aztlek/ModularCockpit/modules/MovementModule/README.md

# Movement Module

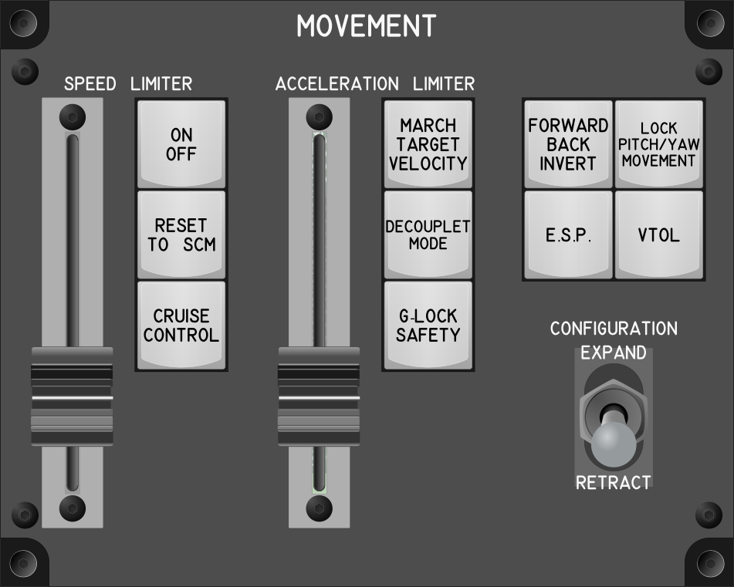
[picture p10: modules/MovementModule/images/MovementModule_150mmWidth.png]
Movement Module


## Keybindings

| Keybinding |  Key / Mouse  | Joy  | Input Device Type |
| --- | --- | ---- | --- |
| Strafe forward / back Invert | | Key  | key[0] |
| Decouplet mode (toggle) | Left Alt + C  | Key  | key[1] |
| Speed Limiter (Abs.) | | Axis | slide_pot[0] |
| Speed Limiter - On/Off (Hold/Toggle) | | Key  | key[2] |
| Speed Limiter – Reset to SCM | | Key  | key[3] |
| Acceleration Limiter Up / Down (abs.) | | Axis | slide_pot[1] |
| March target velocity | | Key  | key[4] |
| Lock Pitch / Yaw movement (toggle / hold) | Right Shift | Key  | key[5] |
| G-Lock safety On/Off (Toggle / Hold) | | Key  | key[6] |
| E.S.P. On/Off (Toggle / Hold) | | Key  | key[7] |
| @ui+v_ifcs_esp_hold | | Key  | key[8] |
| Cruise Control (Toggle) | C | Key  | key[9] |
| Toggle VTOL | K | Key  | key[10] |
| Expand Configuration | | Key  | toggle_switch[0]: On  |
| Retract Configuration | | Key  | toggle_switch[0]: Off |

### Total devices in keybindings

| Device | Count  |
| --- | -----: |
| Keys | 11 |
| Toggle switchs | 1 |
| Encoders | 0 |
| Slide Pot | 2 |
| Joystick | 0 |

## Bill of materials

| Material | Qty. | Links |
| --- | ---: | --- |
| Twidec/Heavy Duty Rocker Toggle Switch 16A 250V SPST 2 Position 2 Pin ON/Off Switch with Black PC Wear-Resistant Handle TEN-A-2210BK-A101 | 1 | [Amz](https://www.amazon.com/dp/B07VJ4GQPW) |
| Jade Kailh Box Key Switches | 10 | [Amz (One Package)](https://www.amazon.com/dp/B09WYV6MTJ), [Amz (One Package)](https://www.amazon.com/dp/B0B9BDM57S) |
| Slide Pot - X-Large (10k Linear Taper) | 2 | [Sparkfun](https://www.sparkfun.com/slide-pot-x-large-10k-linear-taper.html) |
| Slide Potentiometer Knob - X-Large | 2 | [Sparkfun](https://www.sparkfun.com/slide-potentiometer-knob-x-large.html), [Amz](https://www.amazon.com/Electronics123-com-Inc-Slide-Potentiometer-Knob/dp/B01K2BZLA0) |
| Teensy 4.0 | 1 | [Amz](https://www.amazon.com/dp/B07W5J3WNH) |
| Terminal Block Breakout Board Module for Teensy 4.0, Screw Mount Version | 1 | [Amz](https://www.amazon.com/dp/B08R7PVCFN) |
| Female to Female Thread Spacer Screws Brass Hex Standoff M3 x 60mm | 4 | [Amz](https://www.amazon.com/dp/B09V272N1N) |
| 3Mx6 Socket Head Cap Bolts | 4 | 1 package[Amz](https://www.amazon.com/dp/B00W8YSCIS) |
| 3M Flat Washers | 8 | In one package [Amz](https://www.amazon.com/dp/B08CHHLQQS) |
| 3Mx12 Button Head Socket Cap Bolts | 2 | In one package [Amz](https://www.amazon.com/dp/B08CHHLQQS) |
| 3Mx5 Button Head Socket Cap Bolts | 4 | In one package [Amz](https://www.amazon.com/dp/B08CHHLQQS) |
| Plastic Primer | 1 | [mtn](https://www.montanacolors.com/en/productos/mtn-pro-plastic-primer-spray/) |
| Black Matte Paint R-9011 | 1 | [mtn](https://www.montanacolors.com/en/productos/mtn-94-aerosol-spray-paint/) |
| 2mm white acrylic | 1 | |
| 3mm translucent acrylic | 1 | |
| 3mm black acrylic | 1 | |
| 3mm black acrylic | 1 | |

## Connections

Drawing Connections

## Key labels

[Key Labels](images/ModuleKeyLabels.pdf)
