aztlek/ModularCockpit/modules/TorretModule/README.md

# Torret Module

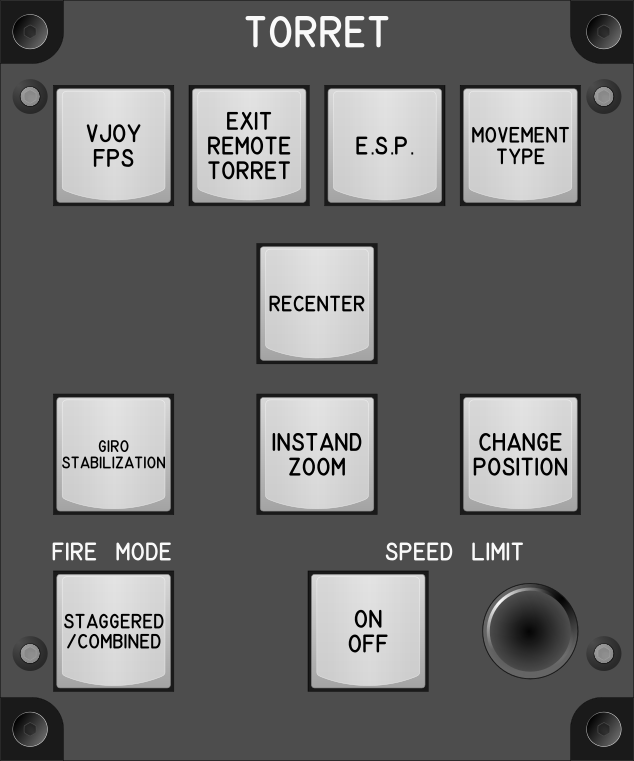
[picture p12: modules/TorretModule/images/TorretModule_100mmWidth.png]
Torret Module


## Keybindings

### Torret Movement

| Keybinding | Input Device Type |
| --- | --- |
| Toggle Torret Mouse Movement (Vjoy, FPS style) | key[0] |
| Exit Remote Torret | key[1] |

### Turret Advanced

| Keybinding | Input Device Type |
| --- | --- |
| Toggle E.S.P.  On/Off | key[2] |
| Recenter Turret | key[3] |
| Turret Giro Stabilization (Toggle) | key[4] |
| Turret Speed Limit On / Off (Toggle / Hold) | key[5] |
| [PH] Turret Speed Limiter  Increase (rel.)  | encoder[0]: increase |
| [PH] Turret Speed Limiter  Decrease (rel.)  | encoder[0]: decrease |
| Cycle Fire Mode (staggered / combined) | key[6] |
| Change prefered movement type | key[7] |
| @ui_CI_InstandZoom | key[8] |
| @ui_ci_turret_change_position | key[9] |

### Total devices in keybindings

| Device |  Count |
| --- | -----: |
| Keys | 10 |
| Toggle switchs | 0 |
| Encoders | 1 |
| Slide | 0 |
| Joysticks | 0 |

## Bill of materials

| Material | Qty. | Links |
| --- | ---: | --- |
| (7 Pin 20MM)10 PCS 360 Degree EC11 Rotary Encoder Code Switch Digital Potentiometer with Caps | 1 | [Amz](https://www.amazon.com/dp/B08BFJ4F5C) |
| Jade Kailh Box Key Switches | 10 | [Amz (One Package)](https://www.amazon.com/dp/B09WYV6MTJ), [Amz (One Package)](https://www.amazon.com/dp/B0B9BDM57S) |3-com-Inc-Slide-Potentiometer-Knob/dp/B01K2BZLA0) |
| Teensy 4.0 | 1 | [Amz](https://www.amazon.com/dp/B07W5J3WNH) |
| Terminal Block Breakout Board Module for Teensy 4.0, Screw Mount Version | 1 | [Amz](https://www.amazon.com/dp/B08R7PVCFN) |
| Female to Female Thread Spacer Screws Brass Hex Standoff M3 x 60mm | 4 | [Amz](https://www.amazon.com/dp/B09V272N1N) |
| 3Mx6 Socket Head Cap Bolts | 4 | 1 package[Amz](https://www.amazon.com/dp/B00W8YSCIS) |
| 3M Flat Washers | 8 | In one package [Amz](https://www.amazon.com/dp/B08CHHLQQS) |
| 3Mx12 Button Head Socket Cap Bolts | 2 | In one package [Amz](https://www.amazon.com/dp/B08CHHLQQS) |
| 3Mx5 Button Head Socket Cap Bolts | 4 | In one package [Amz](https://www.amazon.com/dp/B08CHHLQQS) |
| Plastic Primer | 1 | [mtn](https://www.montanacolors.com/en/productos/mtn-pro-plastic-primer-spray/) |
| Black Matte Paint R-9011 | 1 | [mtn](https://www.montanacolors.com/en/productos/mtn-94-aerosol-spray-paint/) |
| 2mm white acrylic | 1 | |
| 3mm translucent acrylic | 1 | |
| 3mm black acrylic | 1 | |
| 3mm black acrylic | 1 | |

## Connections

Drawing Connections

## Key labels

[Key Labels](images/ModuleKeyLabels.pdf)
