aztlek/ModularCockpit/modules/DockingLandingModule/README.md

# Docking Landing Module

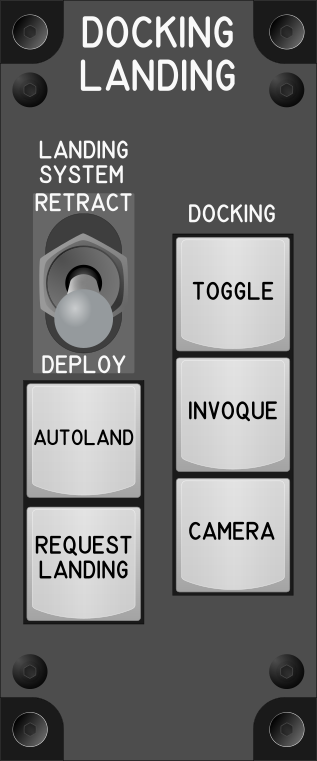
[picture p15: modules/DockingLandingModule/images/DockingLandingModule_50mmWidth.png]
Docking Landing Module


## Keybindings

| Keybinding | Input Device Type |
| ---| --- |
| Toggle Dockin Mode | key[0] |
| Invoque Dockin | key[1] |
| Toggle Docking Camera | key[2] |

### Flight – Movement

| Keybinding | Input Device Type |
| ---| --- |
| Landing System Retract | toggle_switch[2]: on  |
| Landing System Deploy  | toggle_switch[2]: off |
| Request Landing | key[3] |
| Autoland | key[4] |

### Total devices in keybindings

| Device | Count  |
| --- | -----: |
| Keys | 5 |
| Toggle switchs | 1 |
| Encoders | 0 |
| Slide | 0 |
| Joystick | 0 |

## Bill of materials

| Material | Qty. | Links |
| --- | ---: | --- |
| Twidec/Heavy Duty Rocker Toggle Switch 16A 250V SPST 2 Position 2 Pin ON/Off Switch with Black PC Wear-Resistant Handle TEN-A-2210BK-A101 | 1 | [Amz](https://www.amazon.com/dp/B07VJ4GQPW) |
| Jade Kailh Box Key Switches | 5 | [Amz (One Package)](https://www.amazon.com/dp/B09WYV6MTJ), [Amz (One Package)](https://www.amazon.com/dp/B0B9BDM57S) |
| Teensy 4.0 | 1 | [Amz](https://www.amazon.com/dp/B07W5J3WNH) |
| Terminal Block Breakout Board Module for Teensy 4.0, Screw Mount Version | 1 | [Amz](https://www.amazon.com/dp/B08R7PVCFN) |
| Female to Female Thread Spacer Screws Brass Hex Standoff M3 x 60mm | 4 | [Amz](https://www.amazon.com/dp/B09V272N1N) |
| 3Mx6 Socket Head Cap Bolts | 4 | 1 package[Amz](https://www.amazon.com/dp/B00W8YSCIS) |
| 3M Flat Washers | 8 | In one package [Amz](https://www.amazon.com/dp/B08CHHLQQS) |
| 3Mx12 Button Head Socket Cap Bolts | 2 | In one package [Amz](https://www.amazon.com/dp/B08CHHLQQS) |
| 3Mx5 Button Head Socket Cap Bolts | 4 | In one package [Amz](https://www.amazon.com/dp/B08CHHLQQS) |
| Plastic Primer | 1 | [mtn](https://www.montanacolors.com/en/productos/mtn-pro-plastic-primer-spray/) |
| Black Matte Paint R-9011 | 1 | [mtn](https://www.montanacolors.com/en/productos/mtn-94-aerosol-spray-paint/) |
| 2mm white acrylic | 1 | |
| 3mm translucent acrylic | 1 | |
| 3mm black acrylic | 1 | |
| 3mm black acrylic | 1 | |

## Connections

Drawing Connections

## Key labels

[Key Labels](images/ModuleKeyLabels.pdf)
