aztlek/ModularCockpit/modules/MiningModule/README.md

# Mining Module

Mining Module

## Keybindings

### Vehicles – Seats and Operator Modes

| Keybinding | Input Device Type |
| --- | --- |
| Mining Mode (Toggle) | key[0] |

### Vehicles – Mining

| Keybinding | Input Device Type |
| --- | --- |
| Fire Mining Laser (toggle) | key[1] (Mouse Buttton 1) |
| Switch Mining Laser (toggle) | key[2] (Mouse Buttton 2) |
| Increase Mining Laser Power | Encoder[0] (Mouse Wheel Up) |
| Decrease Mining Laser Power | Encoder[0] (Mouse Wheel Down) |
| Activate Mining Module (Slot 1) | key[3] |
| Activate Mining Module (Slot 2) | key[4] |
| Activate Mining Module (Slot 3) | key[5] |
| Jettinson Cargo[^1] | key[6] |

[^1]: That makes?.

### Total devices in keybindings

| Device | Count  |
| --- | -----: |
| Keys | 7 |
| Toggle switchs | 0 |
| Encoders | 1 |

## Bill of materials

| Material | Qty. | Links |
| --- | ---: | --- |
| (7 Pin 20MM)10 PCS 360 Degree EC11 Rotary Encoder Code Switch Digital Potentiometer with Caps | 1 | [Amz](https://www.amazon.com/dp/B08BFJ4F5C) |
| Jade Kailh Box Key Switches | 7 | [Amz (One Package)](https://www.amazon.com/dp/B09WYV6MTJ), [Amz (One Package)](https://www.amazon.com/dp/B0B9BDM57S) |3-com-Inc-Slide-Potentiometer-Knob/dp/B01K2BZLA0) |
| Teensy 4.0 | 1 | [Amz](https://www.amazon.com/dp/B07W5J3WNH) |
| Terminal Block Breakout Board Module for Teensy 4.0, Screw Mount Version | 1 | [Amz](https://www.amazon.com/dp/B08R7PVCFN) |
| Female to Female Thread Spacer Screws Brass Hex Standoff M3 x 60mm | 4 | [Amz](https://www.amazon.com/dp/B09V272N1N) |
| 3Mx6 Socket Head Cap Bolts | 4 | 1 package[Amz](https://www.amazon.com/dp/B00W8YSCIS) |
| 3M Flat Washers | 8 | In one package [Amz](https://www.amazon.com/dp/B08CHHLQQS) |
| 3Mx12 Button Head Socket Cap Bolts | 2 | In one package [Amz](https://www.amazon.com/dp/B08CHHLQQS) |
| 3Mx5 Button Head Socket Cap Bolts | 4 | In one package [Amz](https://www.amazon.com/dp/B08CHHLQQS) |
| Plastic Primer | 1 | [mtn](https://www.montanacolors.com/en/productos/mtn-pro-plastic-primer-spray/) |
| Black Matte Paint R-9011 | 1 | [mtn](https://www.montanacolors.com/en/productos/mtn-94-aerosol-spray-paint/) |
| 2mm white acrylic | 1 | |
| 3mm translucent acrylic | 1 | |
| 3mm black acrylic | 1 | |
| 3mm black acrylic | 1 | |

## Connections

Drawing Connections

## Key labels

[Key Labels](images/ModuleKeyLabels.pdf)
