aztlek/ModularCockpit/modules/OnFootModule/README.md

# On Foot Module

## Keybindings

### On Foot

#### Movement On Foot

| Keybinding |  Key / Mouse | Joy  | Input Device Type |
| --- | --- | ---- | --- |
| Jump | Spacebar | Key  |
| Crouch | Left Ctrl | Key  |
| Prone | X | Key  |
| Roll Lefth (while Prone) | Q (Double Tab) | Axis |
| Roll Right (while Prone) | E (Double Tab) | Axis |
| Sprint | Left Shift | Key  |
| Walk | | Key  |
| Lean Left | Q | Key  |
| Lean Right | E | Key  |
| Default Movement Speed Increase | Mouse Wheel Up | Key  |
| Default Movement Speed Decrease | Mouse Wheel Down | Key  |
| Hold Breath (ADS) | Left Shift | Key  |

#### Melee On Foot

| Keybinding |  Key / Mouse | Joy  | Input Device Type |
| --- | --- | ---- | --- |
| Select Melee | 5 | Key  |
| Melee – Attack Light Left | Button 1 (mouse) | Key  |
| Melee – Attack Light Right | Button 2 (mouse) | Key  |
| Melee – Attack Heavy Left (Hold) | Button 1 (mouse) | Key  |
| Melee – Attack Heavy Right (Hold) | Button 2 (mouse) | Key  |
| Melee – Block (Hold) | Button 1+2 (mouse) | Key  |
| Melee – Attack (Ranged Weapon + Takedown) | Button 3 (mouse) | Key  |
| Dodge left | A (Double Tab) | |
| Dodge right | D (Double Tab) | |
| Dodge back | S (Double Tab) | |

#### Unarmed Combat On Foot

| Keybinding |  Key / Mouse | Joy  | Input Device Type |
| --- | --- | ---- | --- |
| Unarmed Combat | 0 | Key  |
| Throw – Overarm & Two Handed | Button 1 (mouse) | Key  |
| Throw – Underarm | Button 2 (mouse) | Key  |

#### Firearm On Foot

| Keybinding |  Key / Mouse | Joy  | Input Device Type |
| --- | --- | ---- | --- |
| Firearm – Attack | Button 1 (mouse) | Key  |
| Select Sidearm | 1 | Key  |
| Select Primary Weapon | 2 | Key  |
| Select Secundary Weapon | 3 | Key  |
| Next Weapon | | Key  |
| Previous Weapon | | Key  |
| Reload | R | Key  |
| @ui_CIFSReloadSecunday | | Key  |
| Holster Weapon | R | Key  |
| Customize Weapon | J | Key  |
| Weapon Zeroing Decrease | Page Down | Key  |
| Weapon Zeroing Increase / Auto | Page Up | Key  |
| Change Fire Mode | B | Key  |
| FPS Underbarrel Attachement Action | U | Key  |
| Firearm – Attack | Buttom 1 (mouse) | Key  |
| Aim Down Sight | Button 2 (mouse) | Key  |

#### Equipment and Gadgets On Foot

| Keybinding |  Key / Mouse | Joy  | Input Device Type |
| --- | --- | ---- | --- |
| Select Gadget | 4 | Key  |
| Medical Pen – Inject Other | Button 2 (mouse) | Key  |
| Flashlight (Toggle) | T | Key  |
| Mobliglas (toggle) | F1 | |

#### Tractor Beam

| Keybinding |  Key / Mouse | Joy  | Input Device Type |
| --- | --- | ---- | --- |
| Tractor Beam - Increase Distance | Mouse Wheel Up | Key  |
| Tractor Beam – Decrease Distance | Mouse Wheel Down | Key  |

#### Helmet

| Keybinding |  Key / Mouse | Joy  | Input Device Type |
| --- | --- | ---- | --- |
| Toggle Equipment Helmet | | Key  |
| Helmet | | Key  |
| Wipe Helmet Visor | Left Alt + X | Key  |

#### Items

| Keybinding |  Key / Mouse | Joy  | Input Device Type |
| --- | --- | ---- | --- |
| Drop Item | | Key  |
| Inspect Item | | Key  |

### Incapacited On Foot

| Keybinding |  Key / Mouse | Joy  | Input Device Type |
| --- | --- | ---- | --- |
| Request Rescue (shile Incapacited) | M | |
| Regen (while Incapacited) | Backspace | |

#### Varios

| Keybinding |  Key / Mouse | Joy  | Input Device Type |
| --- | --- | ---- | --- |
| @iu_CIFPSMoveLedgeGrab | Spacebar | Key  |
| Select Contract Item | 6 | Key  |
| Port Modification Interact | Buttom 1 (mouse) | Key  |
