aztlek/ModularCockpit/modules/PowerModule/images/engrave/engrave_NoVectorizedText.pdf

Throttle

OFF

Thrusters

OFF

Engines

OFF

Weapons

OFF

Shields

OFF

power

# power
