aztlek/ModularCockpit/modules/WeaponsModule/images/engrave/engrave_VectorizedText.pdf

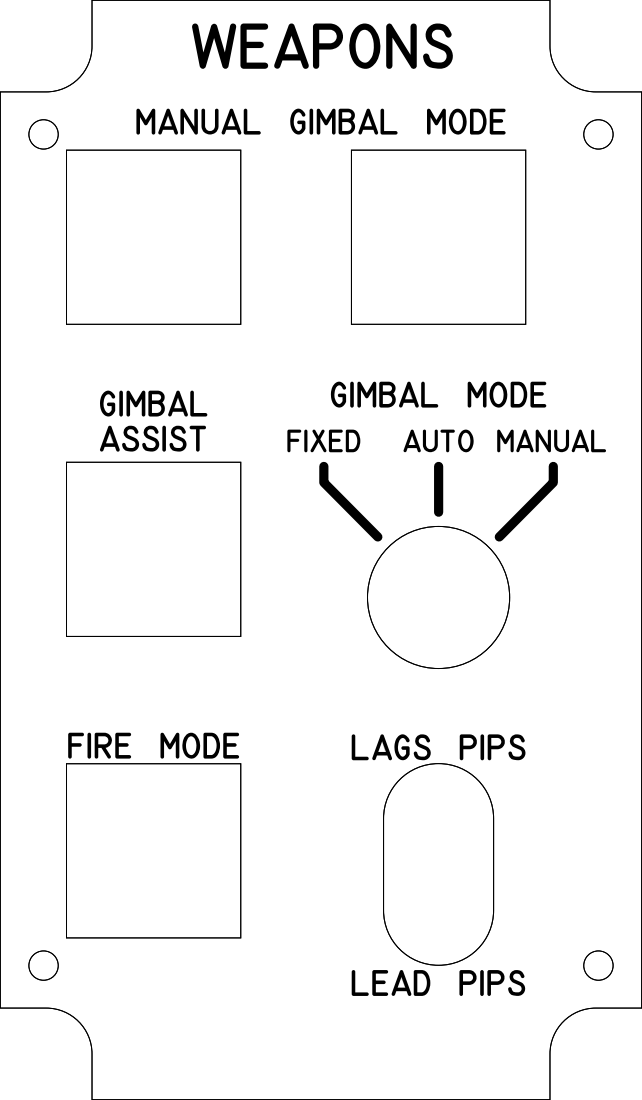
[picture p32: page 1]
