aztlek/ModularCockpit/modules/MovementModule/images/engrave/engrave_VectorizedText.pdf

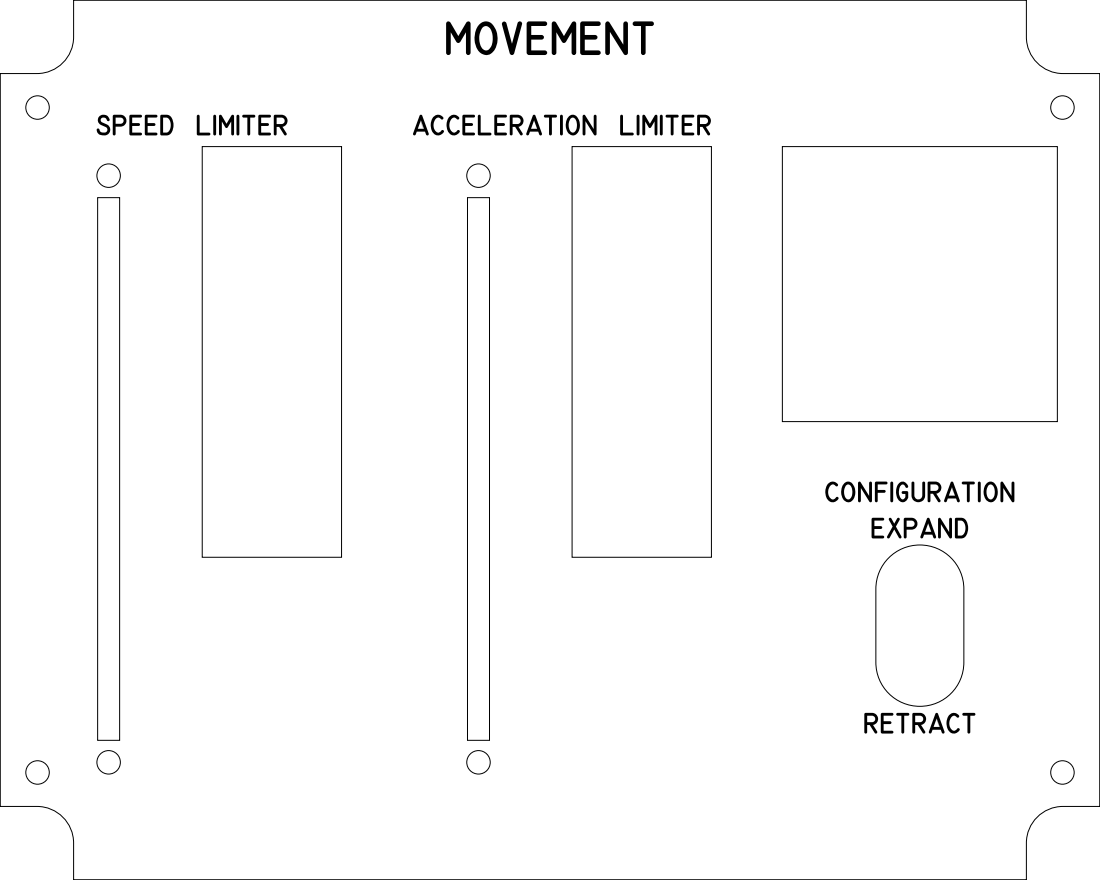
[picture p33: page 1]
