aztlek/ModularCockpit/modules/SalvageModule/images/engrave/engrave_VectorizedText.pdf

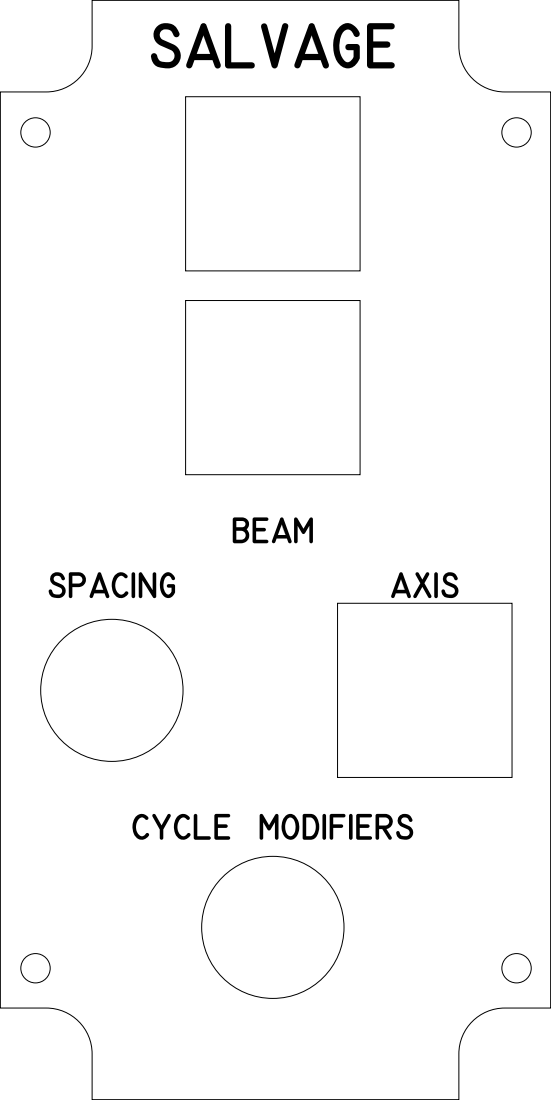
[picture p34: page 1]
