aztlek/ModularCockpit/modules/TargetingModule/images/engrave/engrave_VectorizedText.pdf

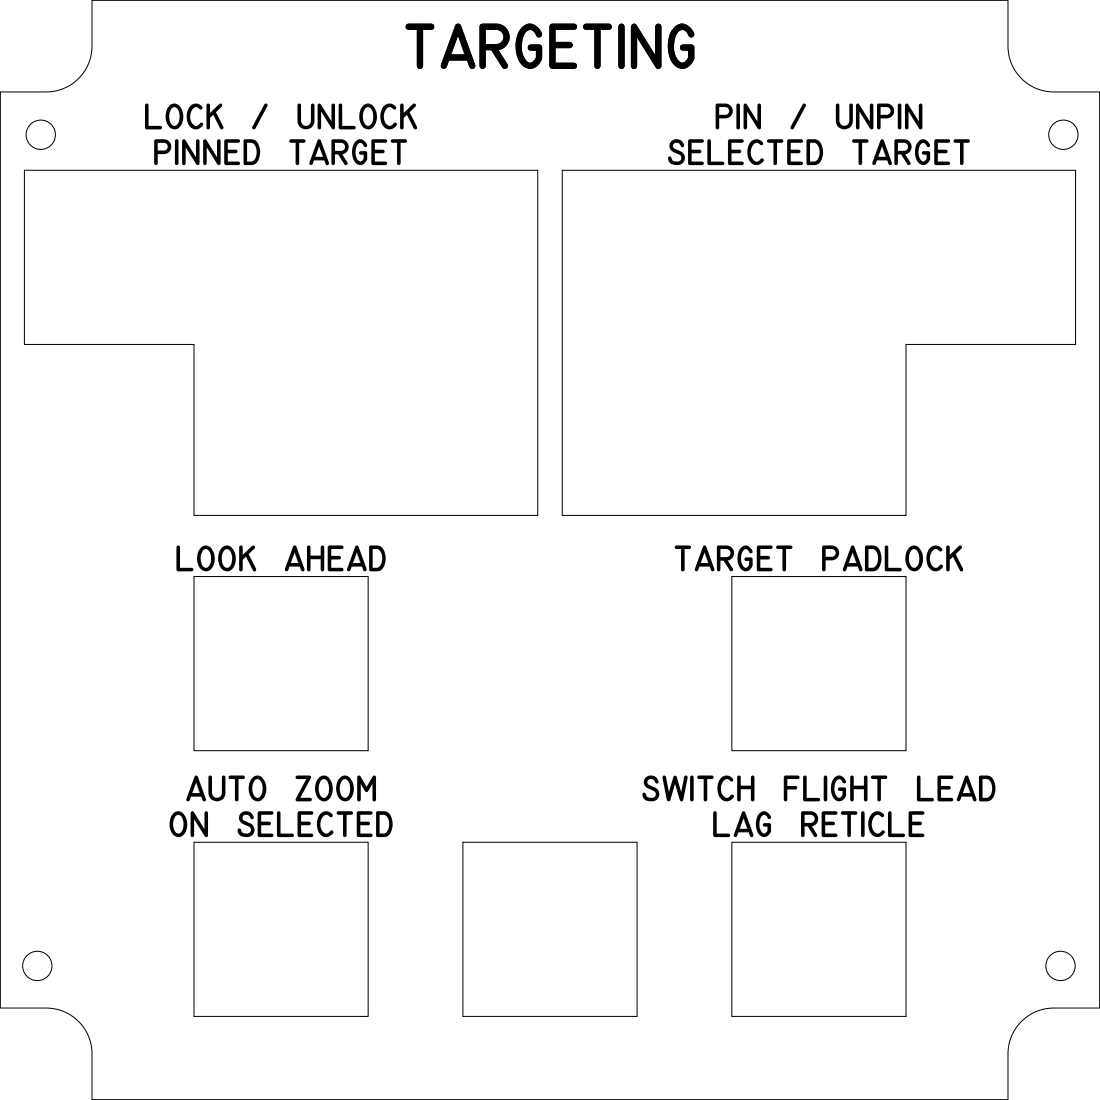
[picture p35: page 1]
