aztlek/ModularCockpit/modules/TargetCyclingModule/images/engrave/engrave_VectorizedText.pdf

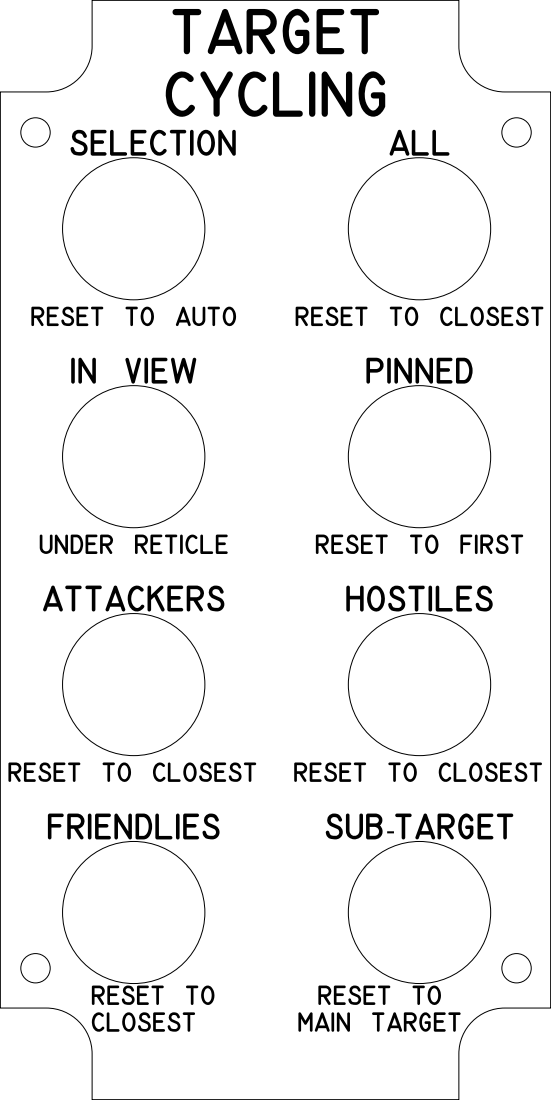
[picture p36: page 1]
