aztlek/ModularCockpit/modules/RadarScanningModule/images/engrave/engrave_VectorizedText.pdf

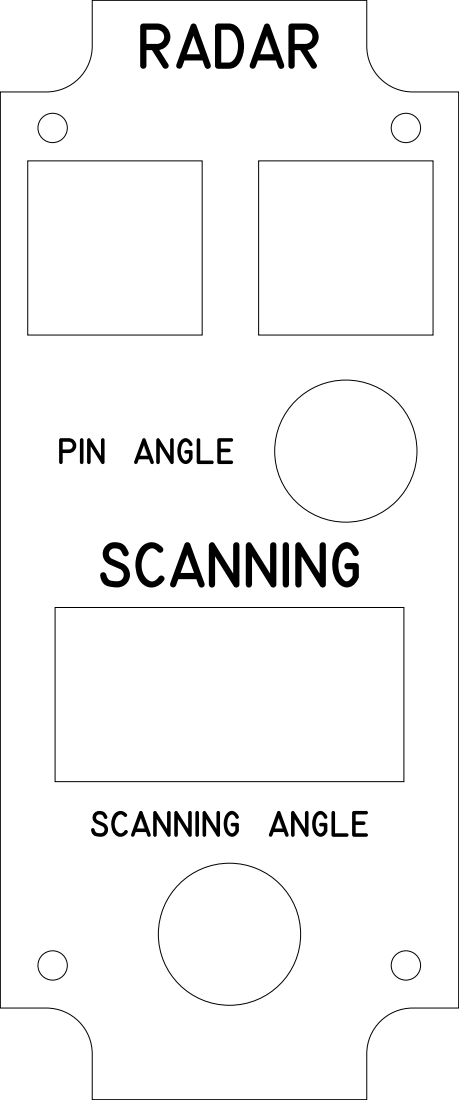
[picture p37: page 1]
