aztlek/ModularCockpit/modules/DockingLandingModule/images/engrave/engrave_VectorizedText.pdf

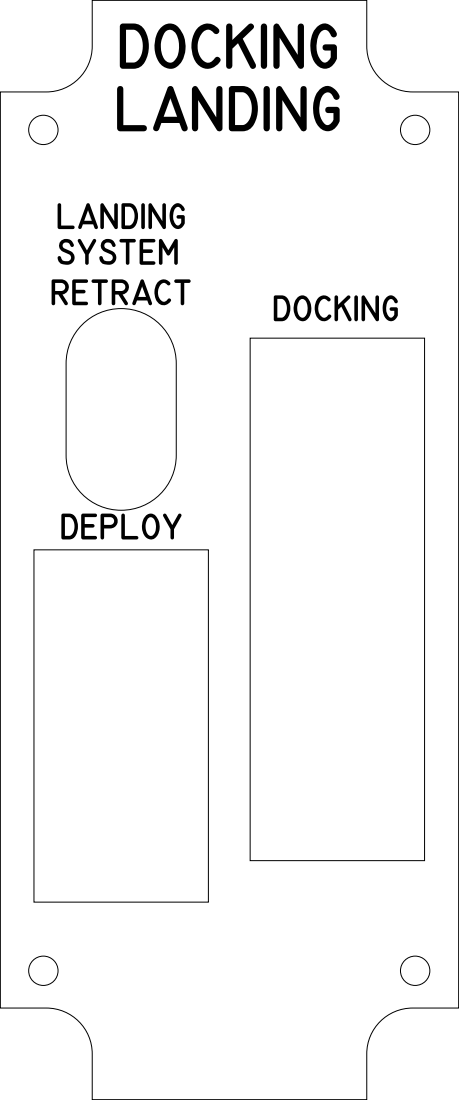
[picture p38: page 1]
