aztlek/ModularCockpit/modules/TorretModule/images/engrave/engrave_VectorizedText.pdf

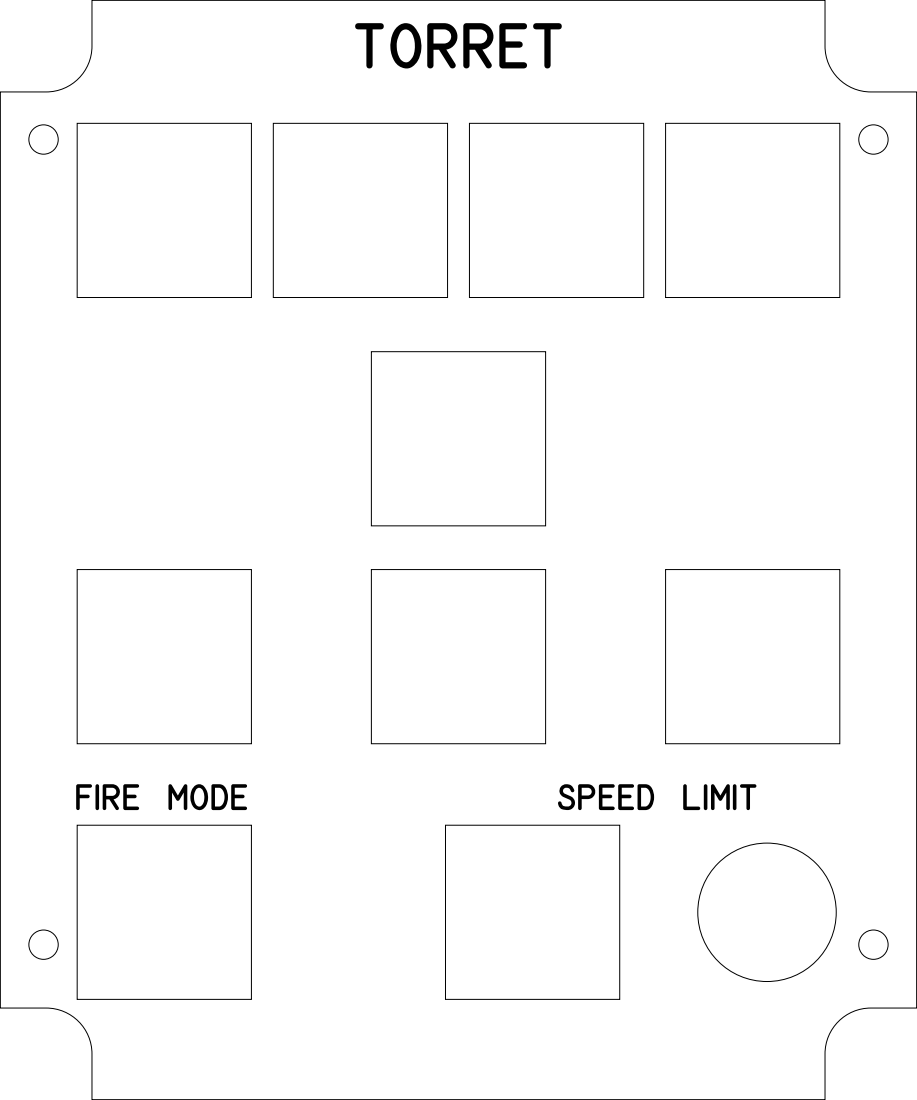
[picture p39: page 1]
