aztlek/ModularCockpit/modules/CameraModule/images/engrave/engrave_VectorizedText.pdf

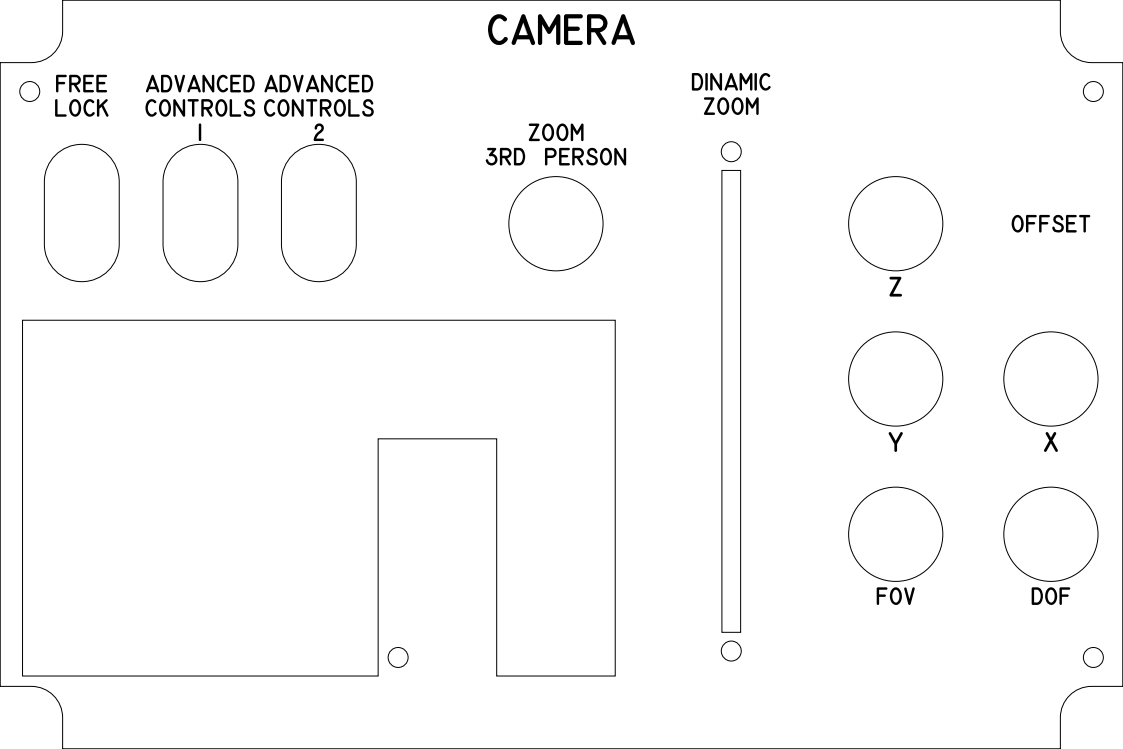
[picture p40: page 1]
