aztlek/ModularCockpit/modules/PowerModule/images/engrave/engrave_VectorizedText.pdf

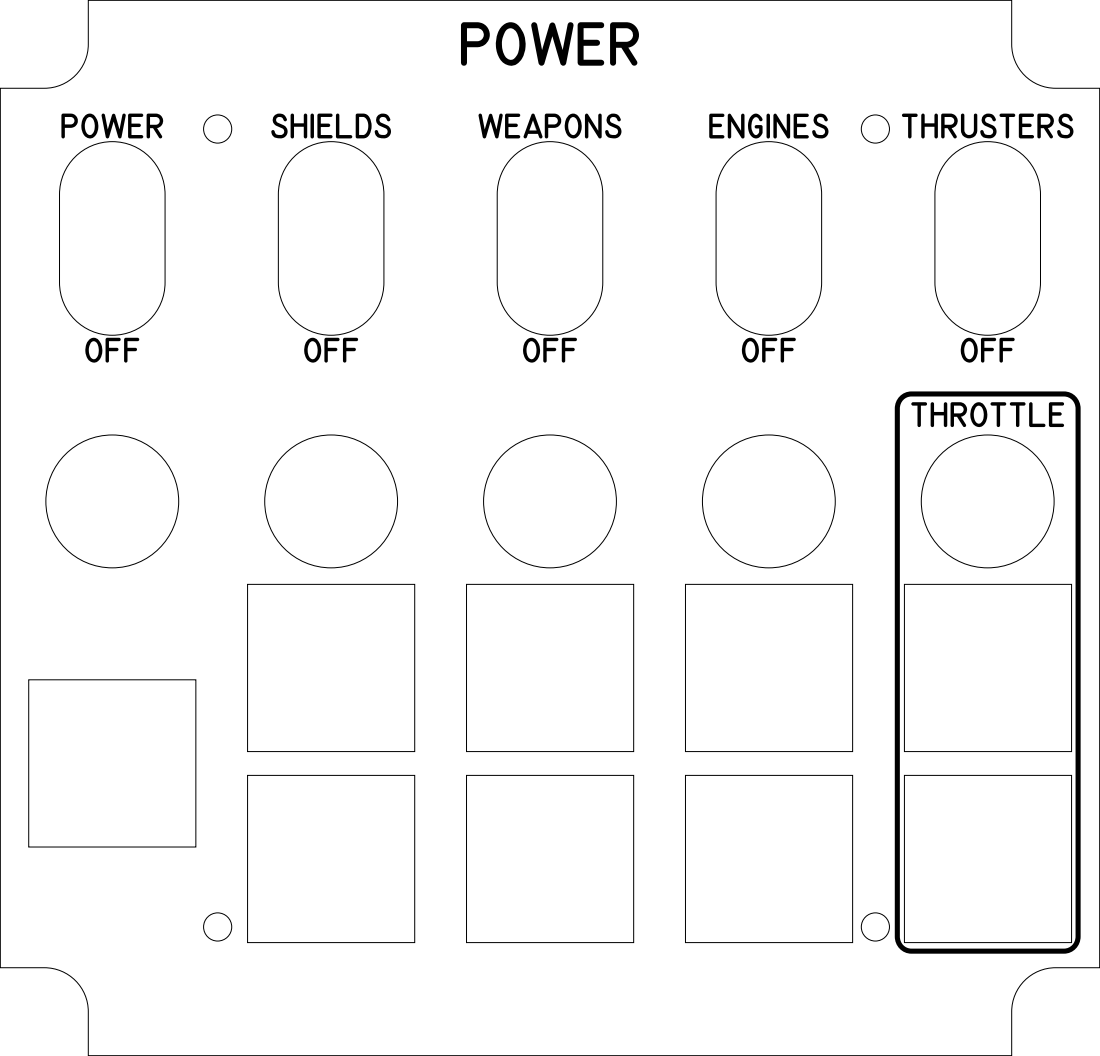
[picture p41: page 1]
