aztlek/ModularCockpit/images/SideView.png

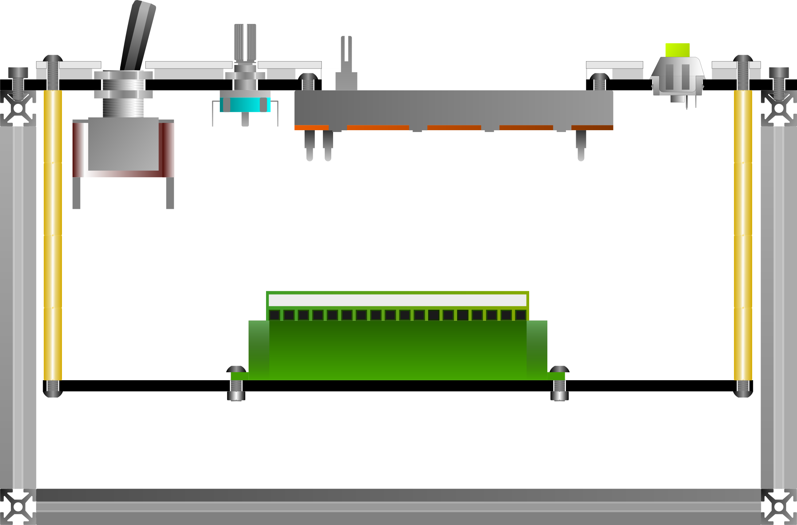
images/SideView.png
