aztlek/ModularCockpit/modules/MiningModule/images/MiningModule_70mmWidth.png

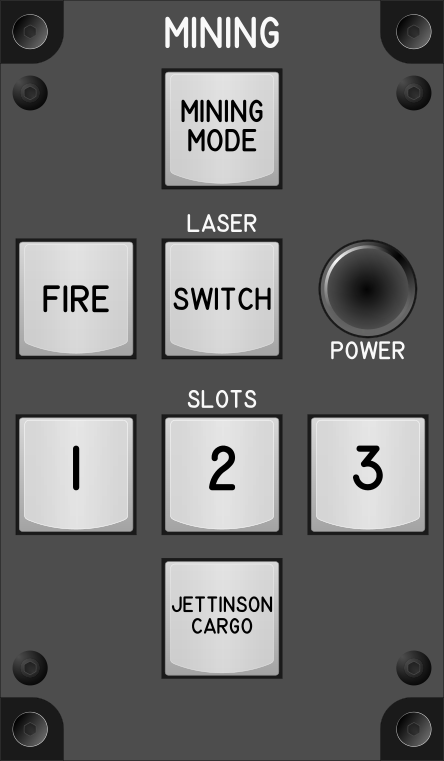
modules/MiningModule/images/MiningModule_70mmWidth.png
