aztlek/ModularCockpit/components/encoder-DaFuRuiEC11/README.md

# Encoder - DaFuRuiEC11

## Views

Side View

Botton View

## Drills

BackLayer Drill
