aztlek/ModularCockpit/components/toggleSwitch-DutyRockerToggleSwitchSPST2Position2PinOnOffSwitchWithBlackPcHandle_TEN-A-2210BK-A101/README.md

# toggleSwitch - Twidec Rocker 2 Pins 2 Position On Off SPSTCarKCD3-101

## Views

Side View

Botton View

## Drills

Front Layer Drill

Middle Layer Drill

BackLayer Drill
