aztlek/ModularCockpit/components/keySwitch-KailhJade/README.md

# Key Switch - Kailh Box Jade

Side View

Bottom View
