aztlek/ModularCockpit/modules/ShieldsCountermeasuresModule/images/engrave/engrave_VectorizedText.pdf

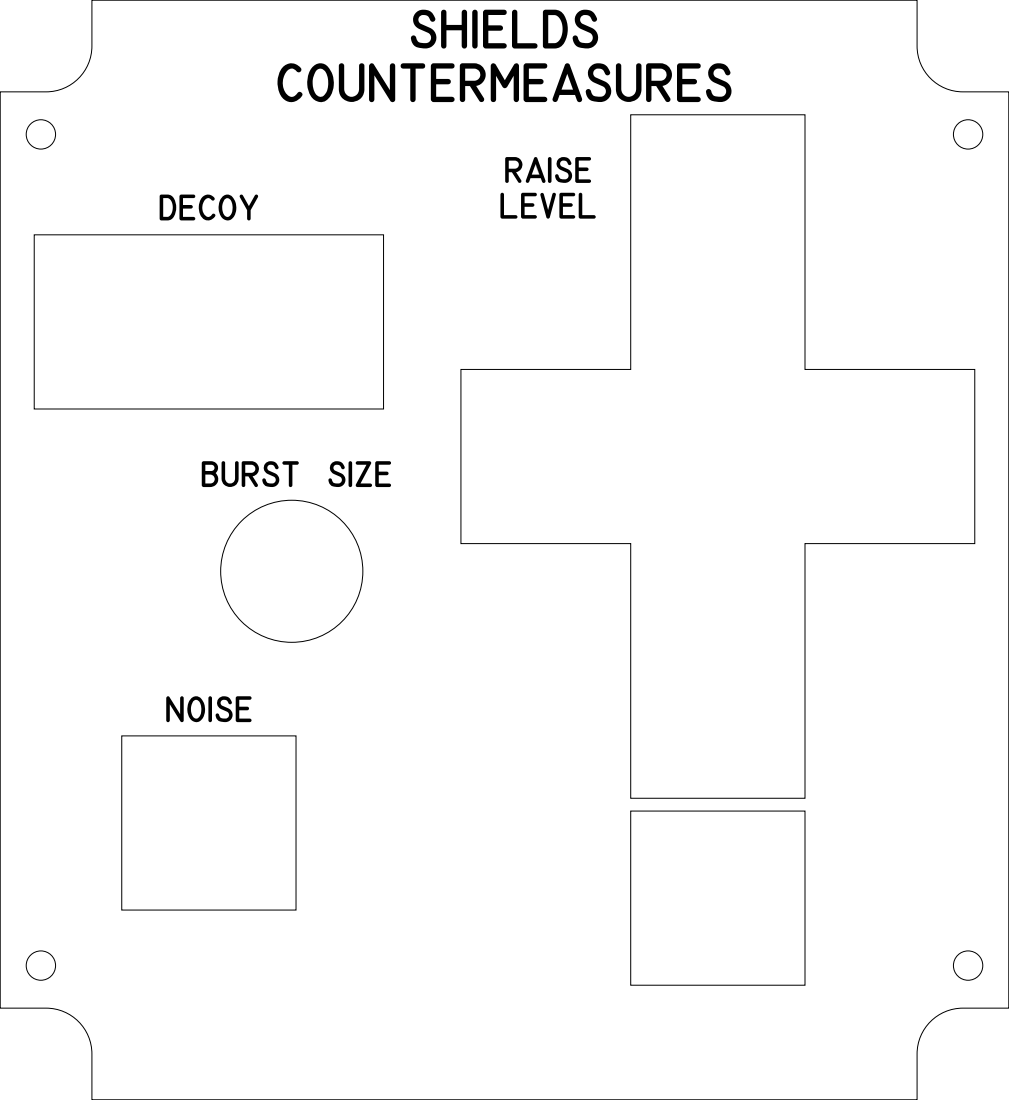
[picture p52: page 1]
