aztlek/ModularCockpit/modules/MovementModule/images/ModuleKeyLabels.pdf

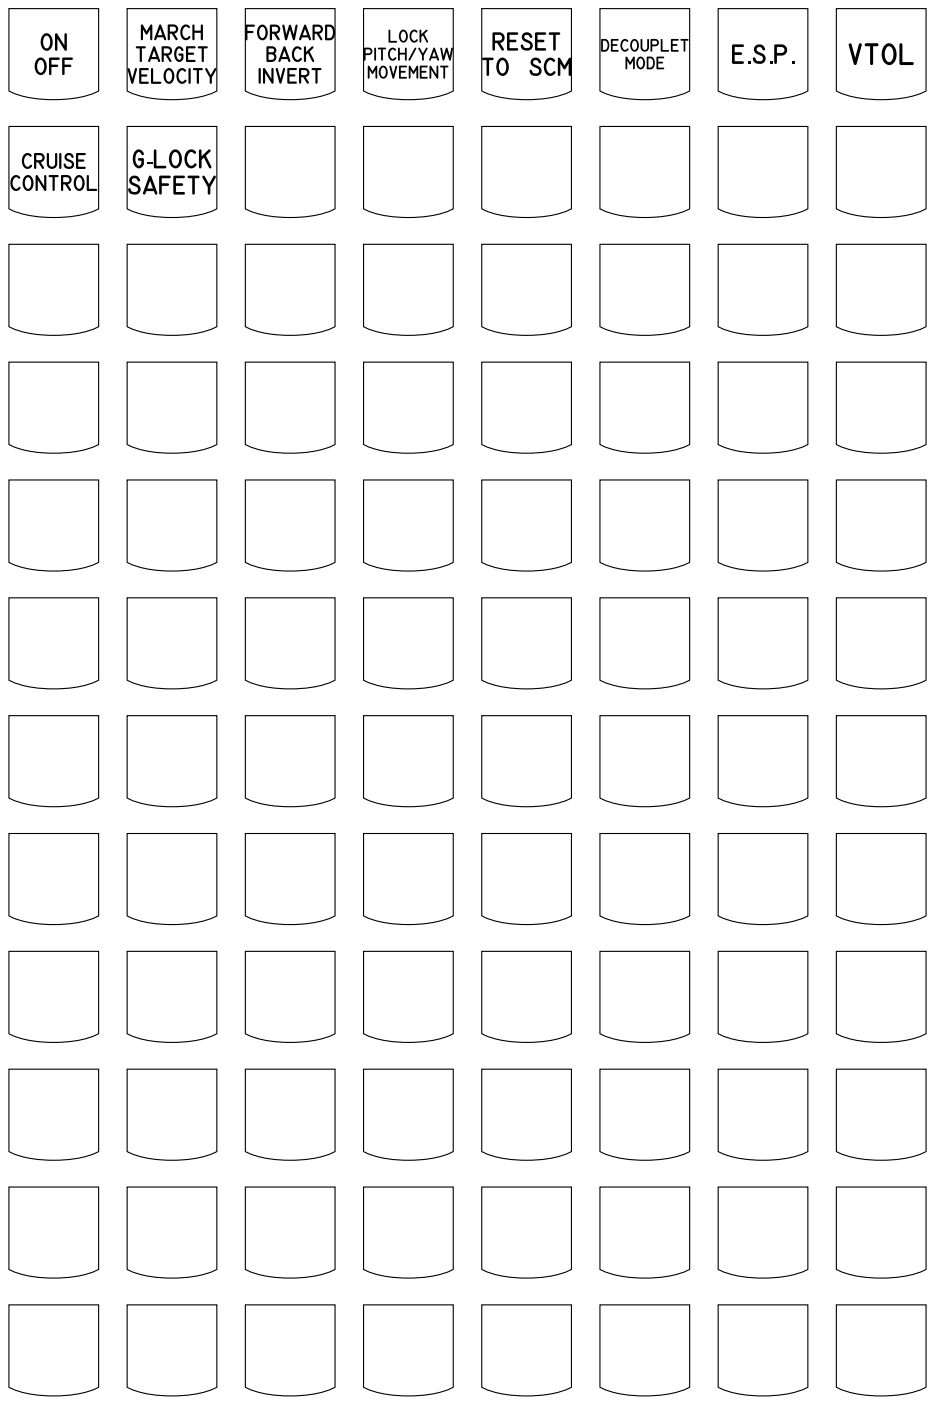
[picture p65: page 1]
