aztlek/ModularCockpit/modules/SalvageModule/images/ModuleKeyLabels.pdf

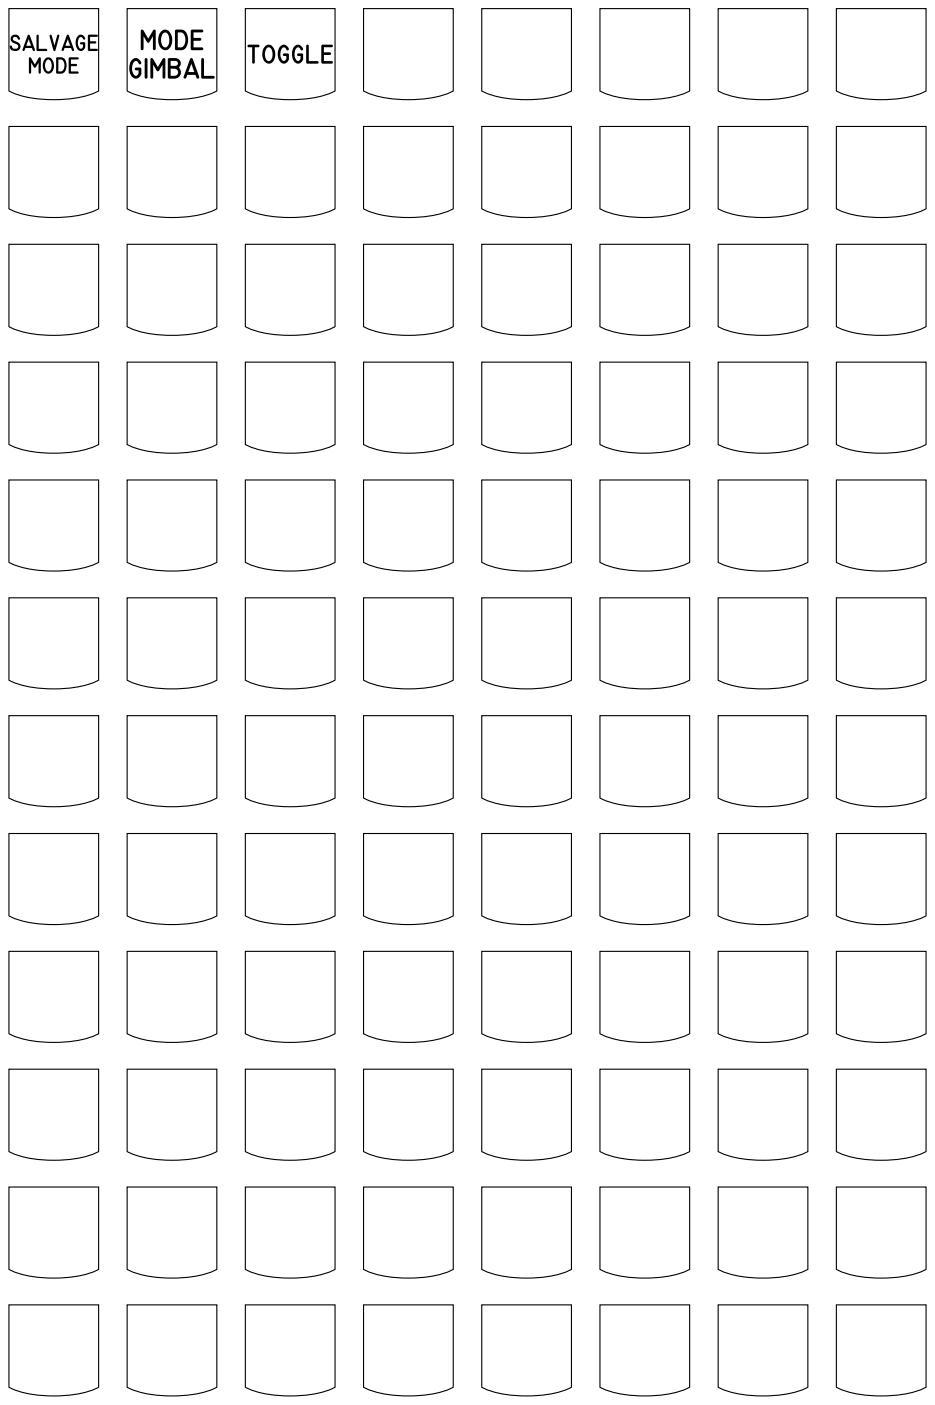
[picture p66: page 1]
