aztlek/ModularCockpit/modules/SocialModule/images/ModuleKeyLabels.pdf

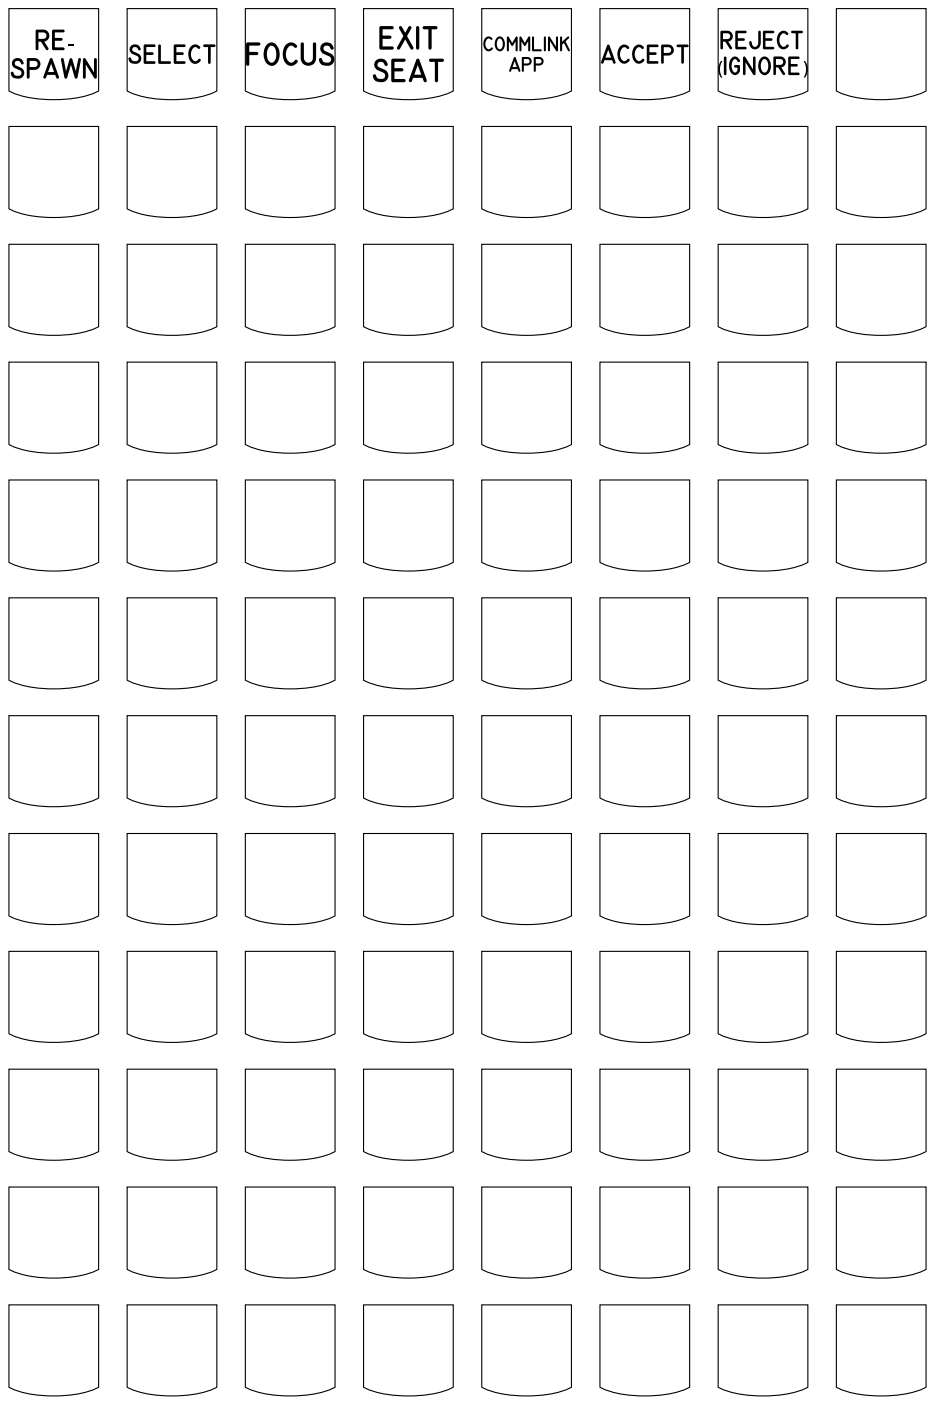
[picture p67: page 1]
