aztlek/ModularCockpit/modules/TargetingModule/images/ModuleKeyLabels.pdf

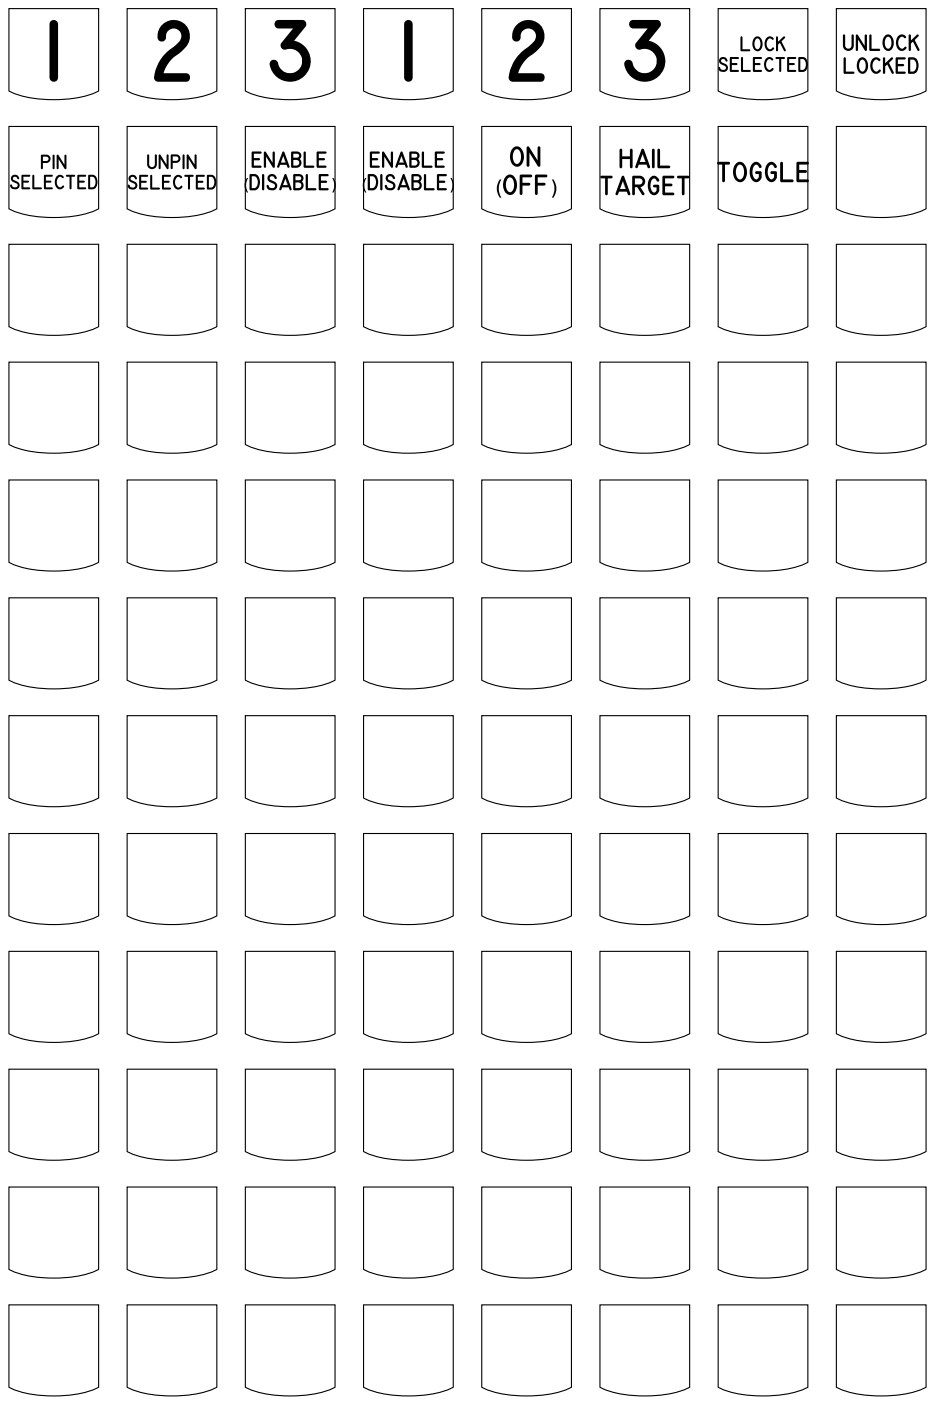
[picture p68: page 1]
