aztlek/ModularCockpit/modules/CameraModule/images/ModuleKeyLabels.pdf

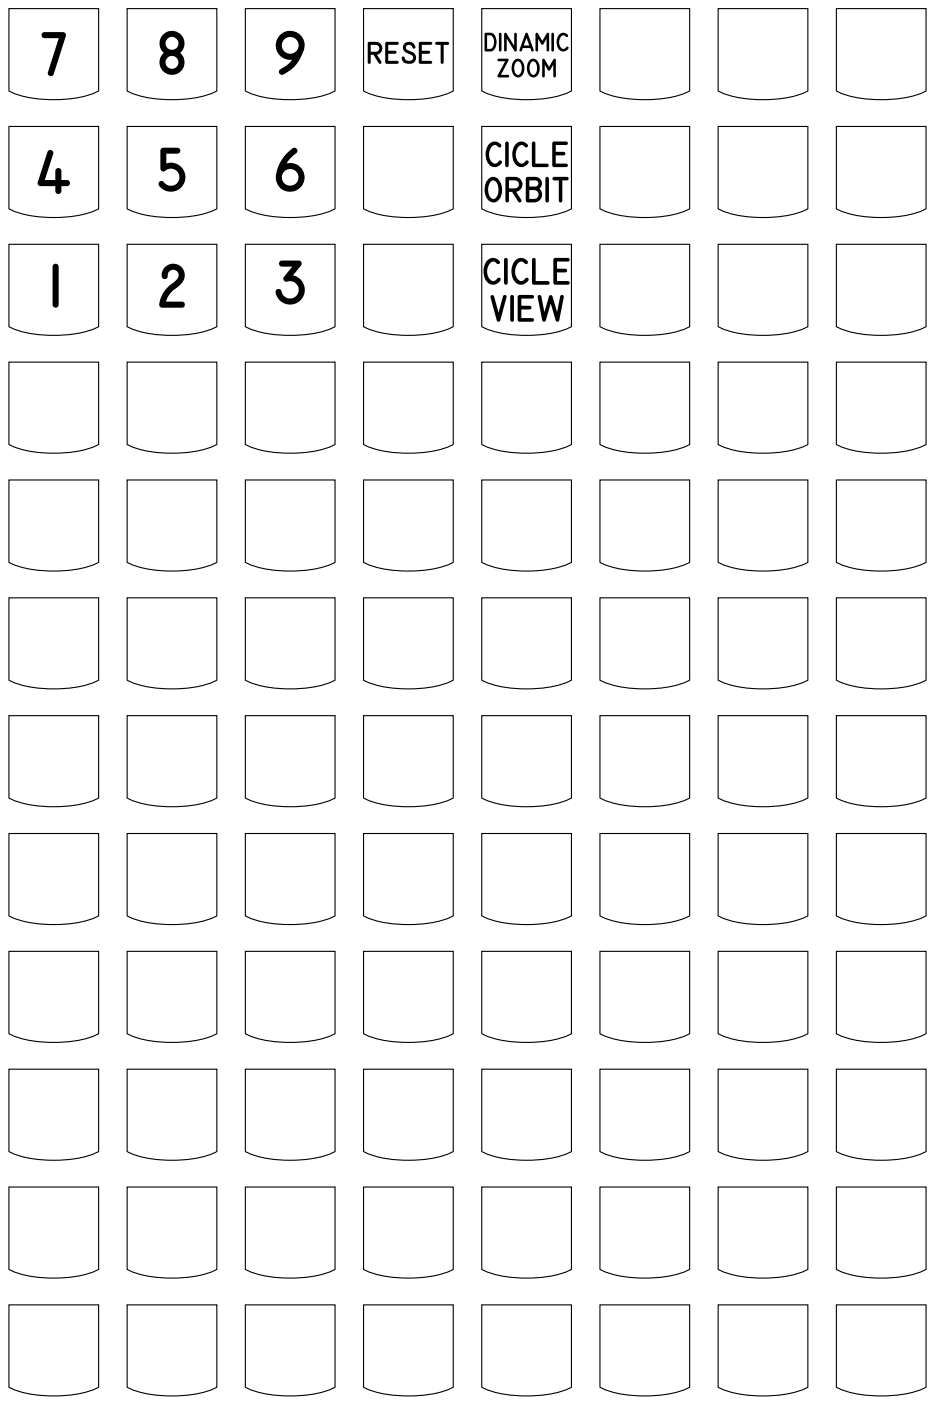
[picture p69: page 1]
