aztlek/ModularCockpit/modules/HudModule/images/ModuleKeyLabels.pdf

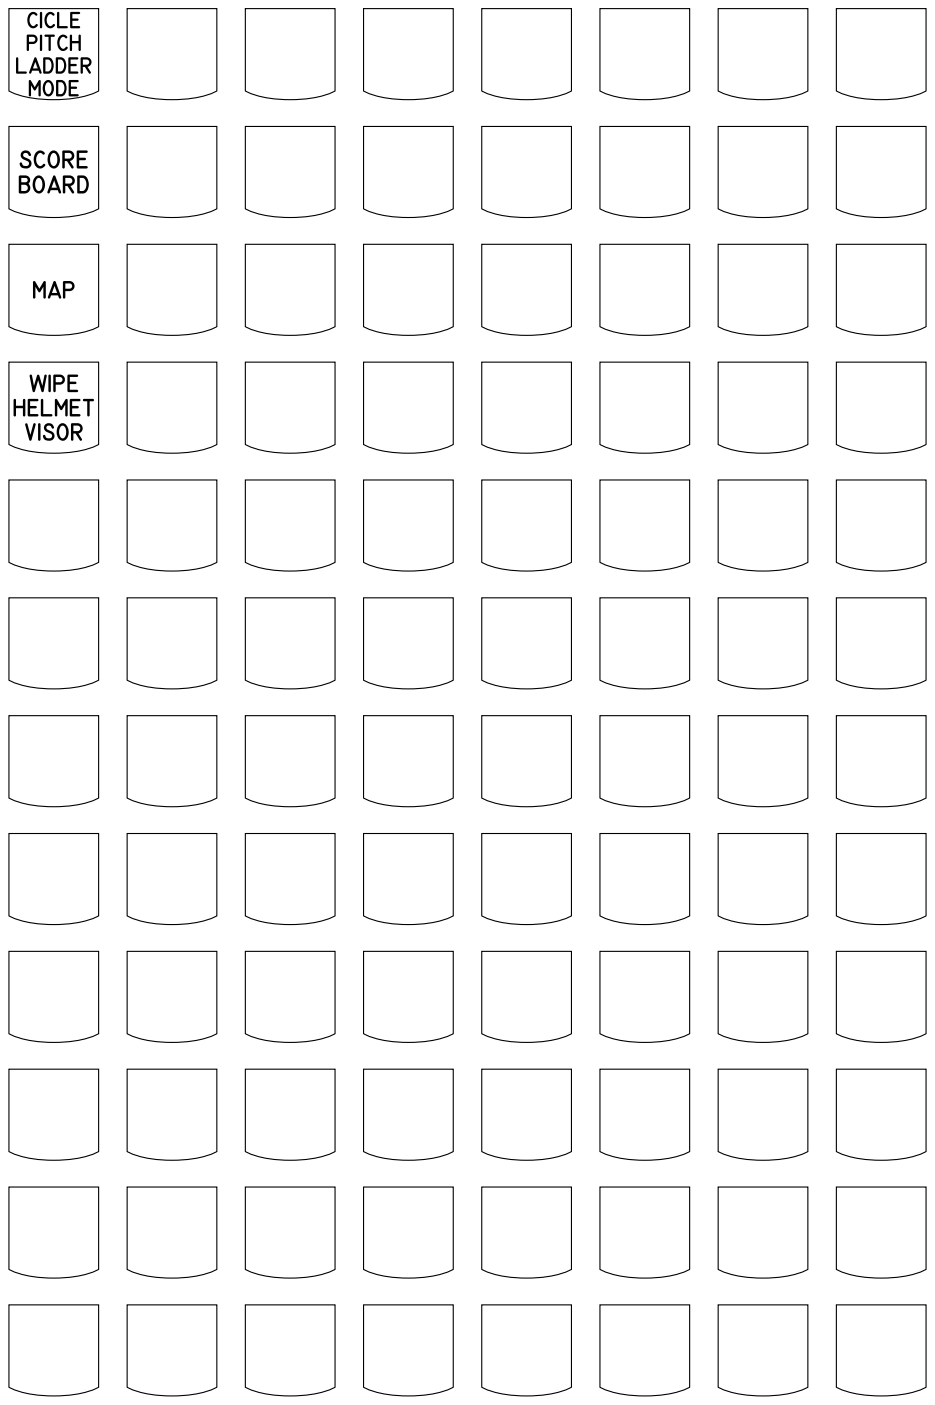
[picture p70: page 1]
