aztlek/ModularCockpit/modules/StopwatchModule/images/engrave/engrave_VectorizedText.pdf

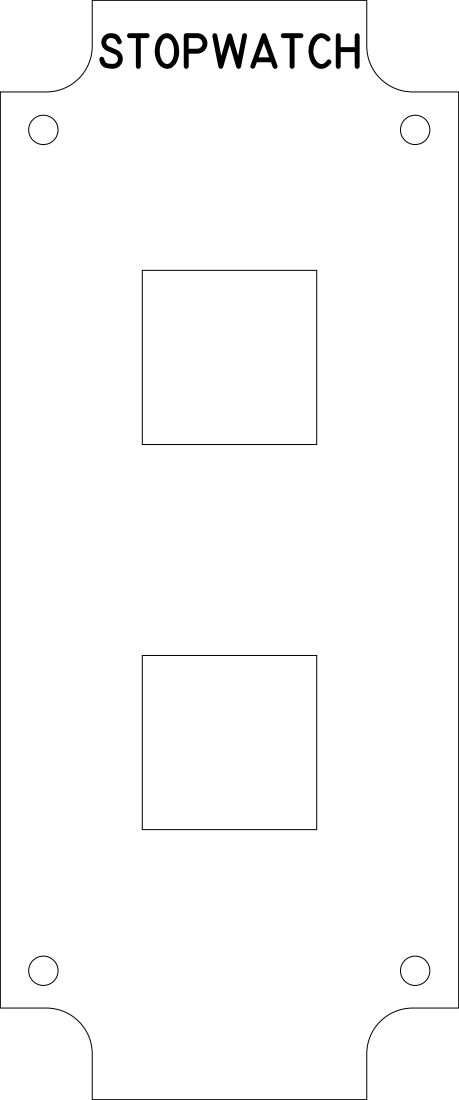
[picture p71: page 1]
