aztlek/ModularCockpit/modules/MiningModule/images/engrave/engrave_VectorizedText.pdf

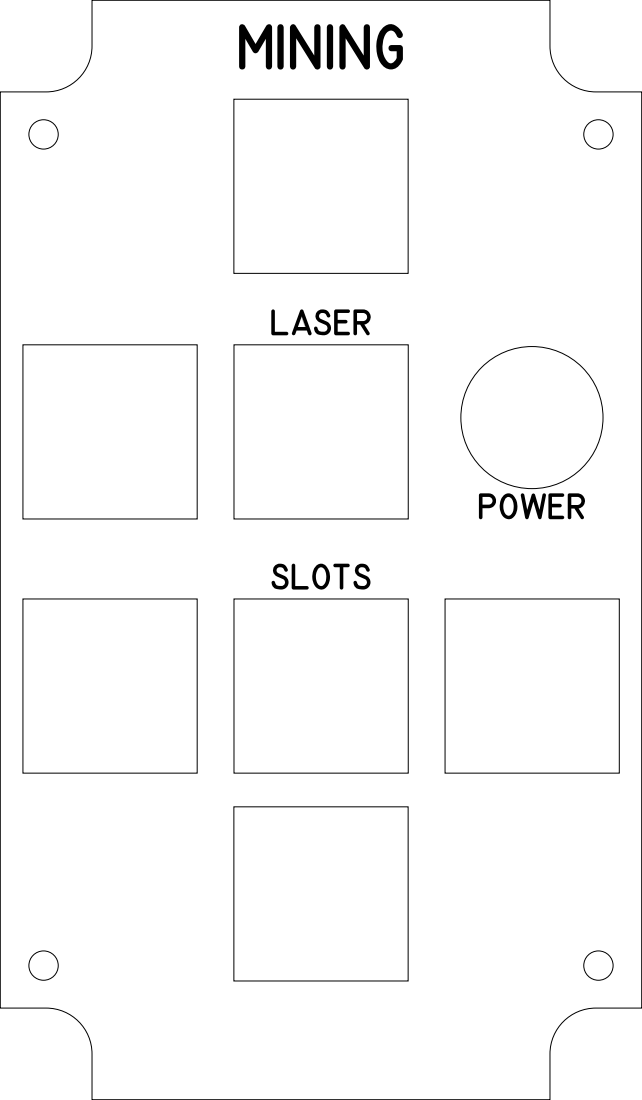
[picture p72: page 1]
