aztlek/ModularCockpit/modules/MissilesModule/images/engrave/engrave_VectorizedText.pdf

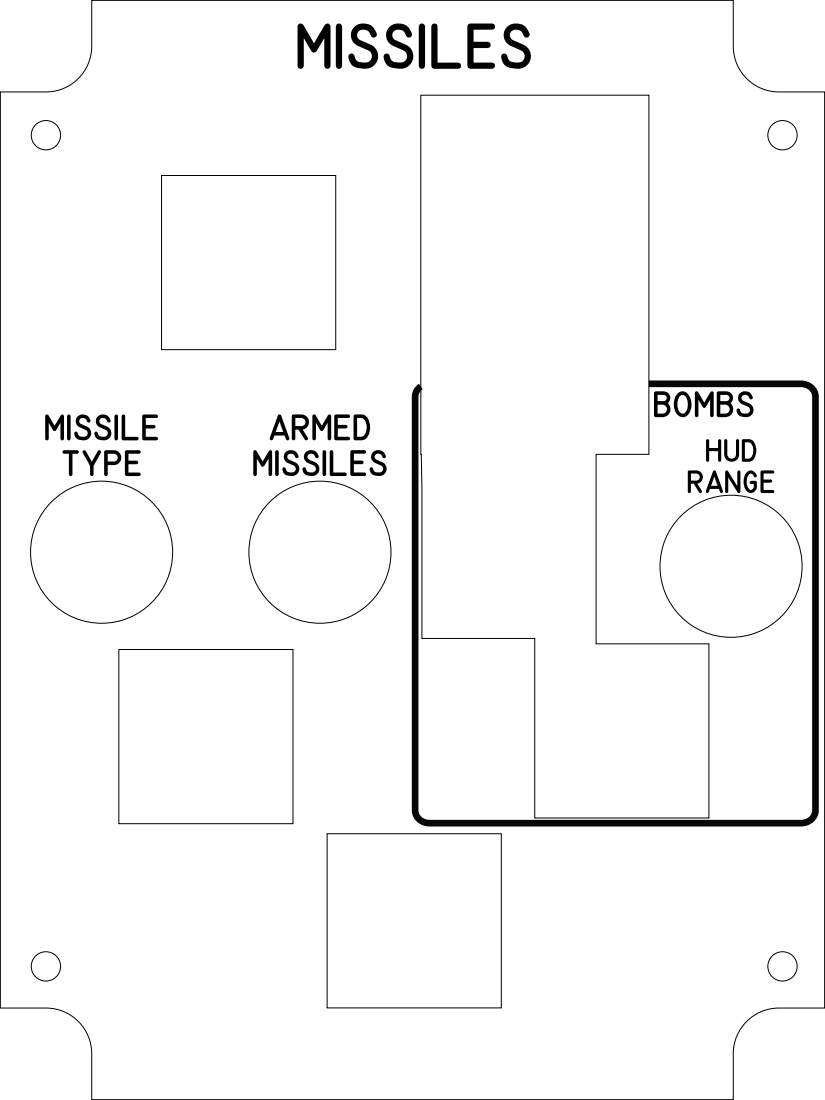
[picture p73: page 1]
