aztlek/ModularCockpit/modules/SocialModule/images/engrave/engrave_VectorizedText.pdf

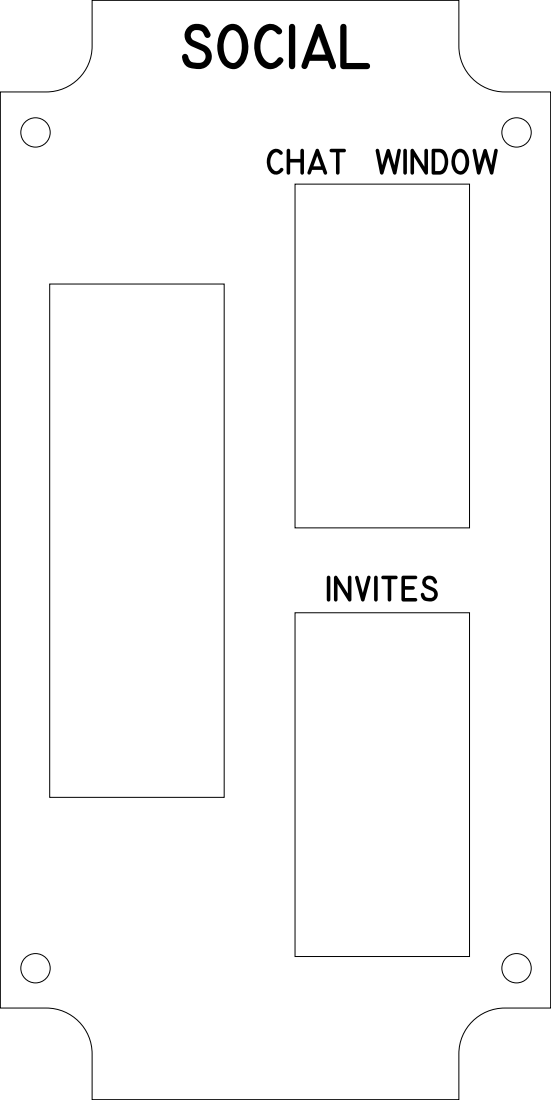
[picture p74: page 1]
