aztlek/ModularCockpit/modules/CockpitModule/images/engrave/engrave_VectorizedText.pdf

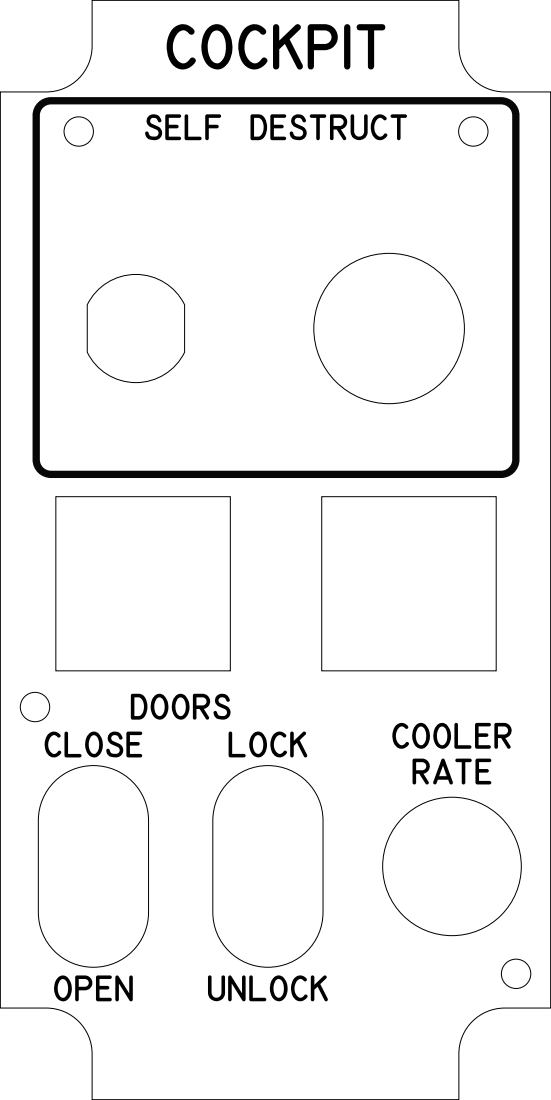
[picture p75: page 1]
