aztlek/ModularCockpit/modules/HudModule/images/engrave/engrave_VectorizedText.pdf

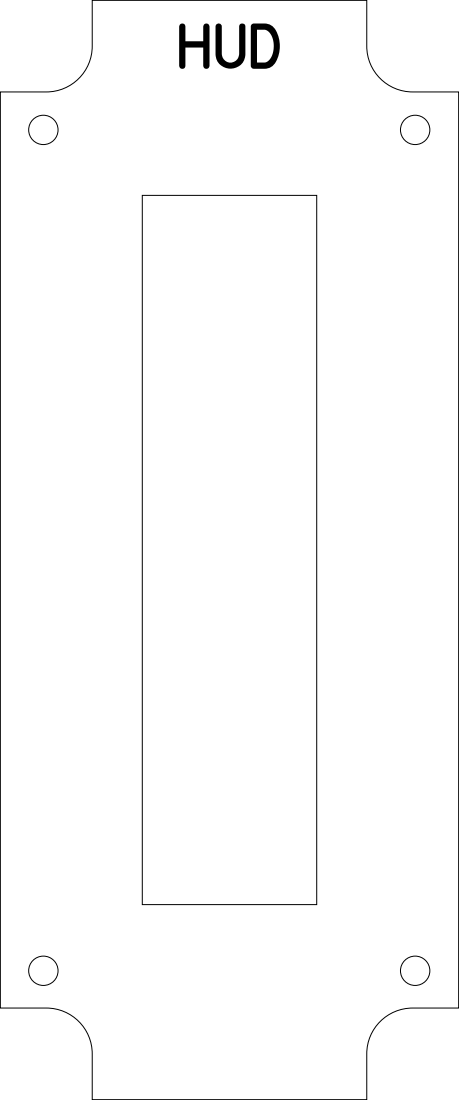
[picture p76: page 1]
