aztlek/ModularCockpit/modules/TorretModule/src/TorretModule-firmware/TorretModule-firmware.ino

/*
||
|| @file firmware.ino
|| @author Luis Alejandro Bernal Romero (Aztlek)
|| @description
|| | This firmware is for the "Torret Module" of the "Modular Cockpit".
|| | @see Power Module: https://github.com/aztlek/ModularCockpit/tree/main/modules/TorretModule
|| | @see Modular Cockpit: https://github.com/aztlek/ModularCockpit.
|| #
|| 
|| @license
|| | Copyright (C) 2020 Luis Alejandro Bernal Romero (Aztlek)
|| | 
|| | This program is free software: you can redistribute it and/or modify
|| | it under the terms of the GNU General Public License as published by
|| | the Free Software Foundation, either version 3 of the License, or
|| | (at your option) any later version.
|| | 
|| | This program is distributed in the hope that it will be useful,
|| | but WITHOUT ANY WARRANTY; without even the implied warranty of
|| | MERCHANTABILITY or FITNESS FOR A PARTICULAR PURPOSE.  See the
|| | GNU General Public License for more details.
|| | 
|| | You should have received a copy of the GNU General Public License
|| | along with this program.  If not, see <http://www.gnu.org/licenses/>.
|| #
||
*/

#include <Bounce.h>
#include <Encoder.h>

// #define DEBUG

#define NUM_BUTTOMS 10

Bounce buttons[NUM_BUTTOMS] = {
  Bounce( 2, 10), // 1
  Bounce( 3, 10), // 2
  Bounce( 4, 10), // 3
  Bounce( 5, 10), // 4
  Bounce( 6, 10), // 5
  Bounce( 7, 10), // 6
  Bounce( 8, 10), // 7
  Bounce( 9, 10), // 8
  Bounce(10, 10), // 9
  Bounce(11, 10), // 10
};

// Keys
#define KEY_PRESS_TIME 150

// Encoders
#define NUM_ENCODERS 1
Encoder encoders[NUM_ENCODERS] = {
  Encoder(23, 22),  // 1 Scanning Angle
};
//                               Pin Angle, Scanning Angle
int inc_encoder[NUM_ENCODERS] = { 11};
int dec_encoder[NUM_ENCODERS] = { 12};
long oldPositionEncoders[NUM_ENCODERS] = { 0};
long newPositionEncoders[NUM_ENCODERS];

const int ledPin = 13;

String msg;
int code;

extern "C" uint32_t set_arm_clock(uint32_t frequency);

void setup() {
  set_arm_clock(24000000);

  // Led as power indicator
  temporarily_increase_led_brightness(1000);

  // Buttoms
  pinMode( 2, INPUT_PULLUP);
  pinMode( 3, INPUT_PULLUP);
  pinMode( 4, INPUT_PULLUP);
  pinMode( 5, INPUT_PULLUP);
  pinMode( 6, INPUT_PULLUP);
  pinMode( 7, INPUT_PULLUP);
  pinMode( 8, INPUT_PULLUP);
  pinMode( 9, INPUT_PULLUP);
  pinMode(10, INPUT_PULLUP);
  pinMode(11, INPUT_PULLUP);
}

void loop() {
  for (unsigned i = 0; i < NUM_BUTTOMS; i++) {
    buttons[i].update();
  }

  for (unsigned i = 0; i < NUM_BUTTOMS; i++) {
    if (buttons[i].fallingEdge()) {
      msg = "ON";
      code = i + 1;
      Joystick.button(code, 1);
      temporarily_increase_led_brightness(20);
#ifdef DEBUG
      Serial.print("buttoms[");
      Serial.print(i);
      Serial.print("]: ");
      Serial.print("Key ");
      Serial.print(code);
      Serial.print(", ");
      Serial.println(msg);
#endif
    }
  }

  for (unsigned i = 0; i < NUM_BUTTOMS; i++) {
    if (buttons[i].risingEdge()) {
      msg = "OFF";
      code = i + 1;
      Joystick.button(code, 0);
      temporarily_increase_led_brightness(20);
#ifdef DEBUG
      Serial.print("buttoms[");
      Serial.print(i);
      Serial.print("]: ");
      Serial.print("Key ");
      Serial.print(code);
      Serial.print(", ");
      Serial.println(msg);
#endif
    }
  }

  // Encoders
  for (int i = 0; i < NUM_ENCODERS; i++) {
    newPositionEncoders[i] = encoders[i].read();
    long difEncoder = newPositionEncoders[i] - oldPositionEncoders[i];
    int key = (difEncoder > 0) ? inc_encoder[i] : dec_encoder[i];
    if (difEncoder != 0) {
      Joystick.button(key, 1);
      delay(KEY_PRESS_TIME);
      Joystick.button(key, 0);
      temporarily_increase_led_brightness(20);
      oldPositionEncoders[i] = newPositionEncoders[i];

#ifdef DEBUG
      Serial.print("encoder[");
      Serial.print(i);
      Serial.print("]: difEncoder=");
      Serial.print(difEncoder);
      Serial.print(", key=");
      Serial.print(key);
      Serial.println();
#endif
    }
  }
}

void temporarily_increase_led_brightness(uint32_t msec) {
  analogWrite(ledPin, 100);
  delay(msec);
  analogWrite(ledPin, 5);
}
